phorton1/Arduino-useless/docs/images/sensor2.jpg

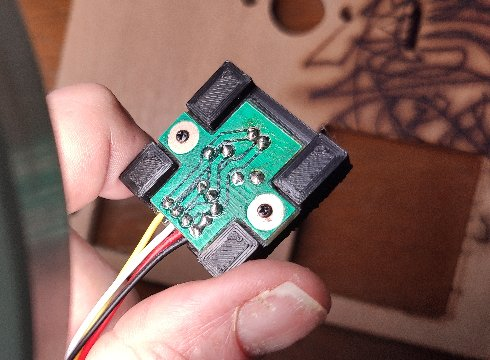
docs/images/sensor2.jpg
