phorton1/Arduino-useless/docs/images/sensor3.jpg

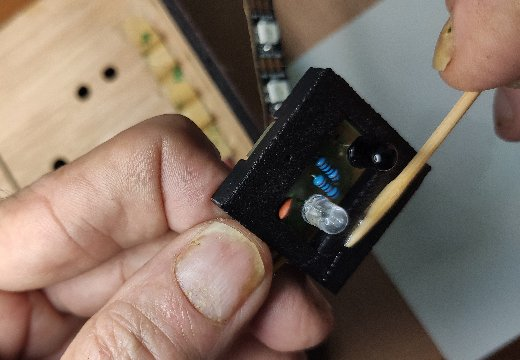
docs/images/sensor3.jpg
