phorton1/Arduino-useless/docs/images/sensor4.jpg

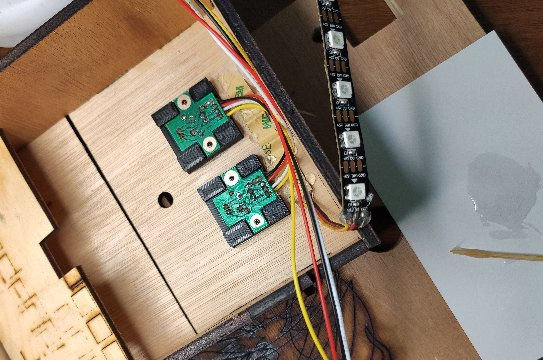
docs/images/sensor4.jpg
