phorton1/Arduino-useless/docs/images/sensor5.jpg

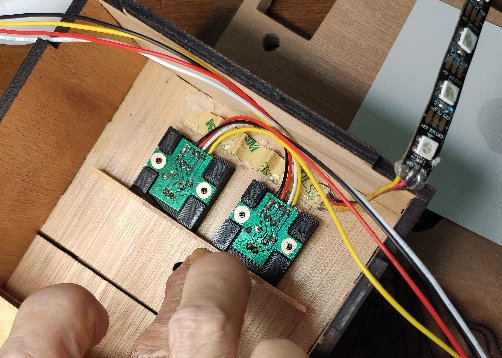
docs/images/sensor5.jpg
