phorton1/Arduino-useless/docs/images/sensor6.jpg

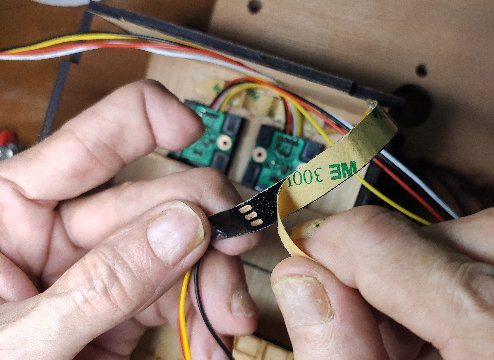
docs/images/sensor6.jpg
