phorton1/Arduino-useless/docs/images/sensor7.jpg

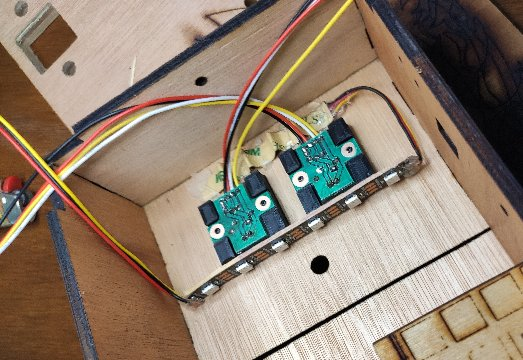
docs/images/sensor7.jpg
