phorton1/Arduino-useless/docs/stl/back_plastic.stl

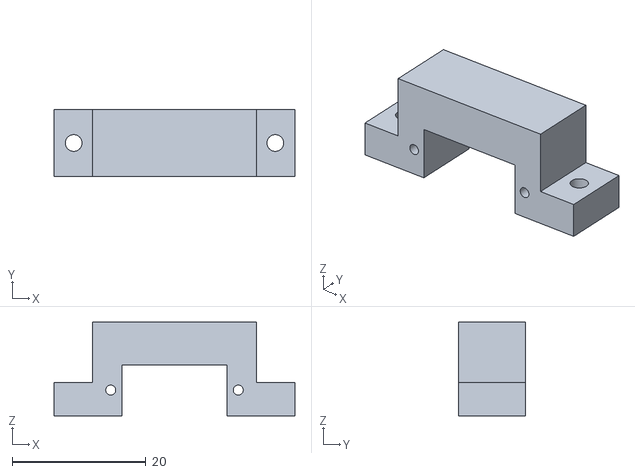
[picture p51: CAD file, 2023-01-01]
docs/stl/back_plastic.stl
36.0 x 10.0 x 14.0
