phorton1/Arduino-useless/docs/stl/front_plastic.stl

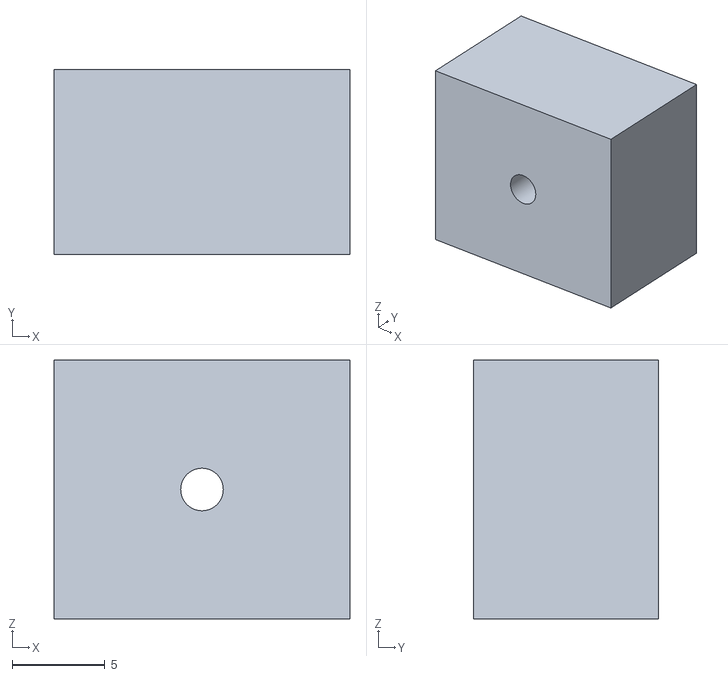
[picture p52: CAD file, 2023-01-01]
docs/stl/front_plastic.stl
16.0 x 10.0 x 14.0
