phorton1/Arduino-useless/docs/stl/lid_guide.stl

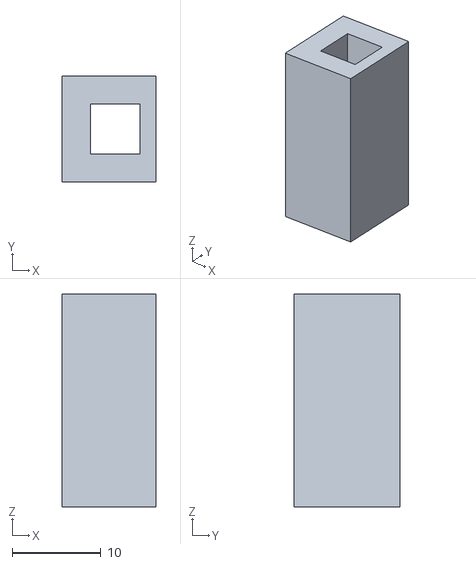
[picture p53: CAD file, 2023-01-01]
docs/stl/lid_guide.stl
10.6 x 12.0 x 24.0
