phorton1/Arduino-useless/docs/dxf/back.dxf

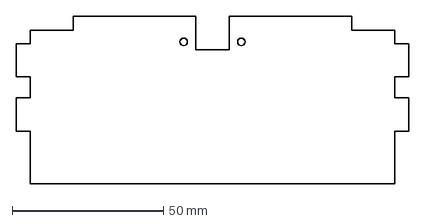
[picture p54: CAD file, 2023-01-01]
docs/dxf/back.dxf
130.0 x 55.4 mm
