phorton1/Arduino-useless/docs/stl/sensor_mount.stl

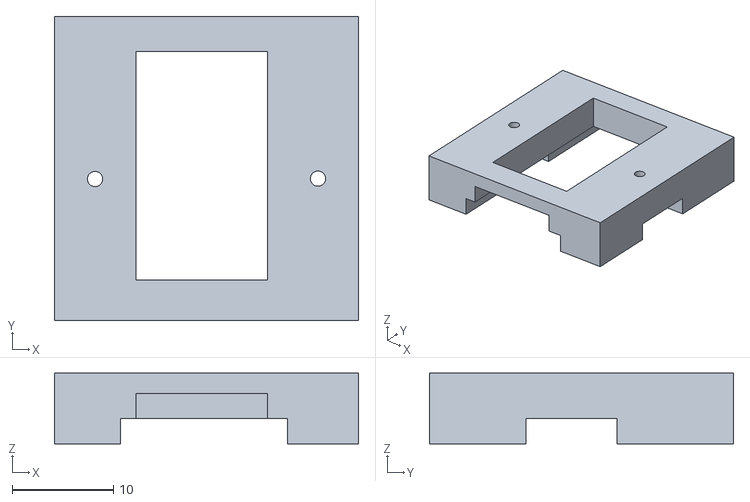
[picture p55: CAD file, 2023-01-01]
docs/stl/sensor_mount.stl
30.0 x 30.0 x 7.00
