phorton1/Arduino-useless/docs/dxf/servo_mount.dxf

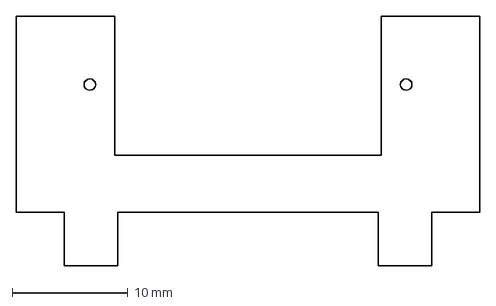
[picture p56: CAD file, 2023-01-01]
docs/dxf/servo_mount.dxf
40.0 x 21.5 mm
