phorton1/Arduino-useless/docs/dxf/front.dxf

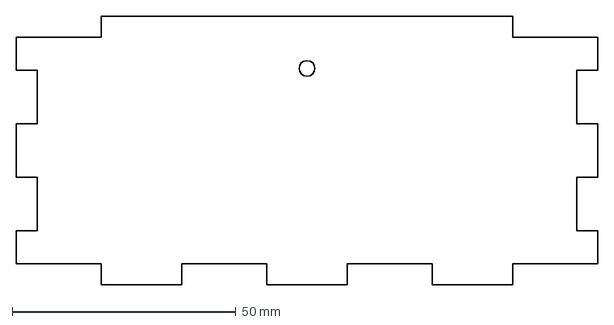
[picture p57: CAD file, 2023-01-01]
docs/dxf/front.dxf
130.0 x 60.0 mm
